vicherarr/camesp32/esp32_cam_sec/src/server.rs

use esp_idf_svc::http::server::{Configuration, EspHttpServer};
use serde::Deserialize;
use esp_idf_svc::http::Method;
use esp_idf_svc::io::Write;
use std::fs;
use std::io::Read;
use anyhow::Result;
use ::log::info;
use std::sync::{Arc, atomic::{AtomicBool, Ordering}};
use esp_idf_svc::nvs::EspDefaultNvsPartition;
use crate::config::{AppConfig, load_config, save_config};

pub struct WebServer {
    _server: EspHttpServer<'static>,
}

/// Capture one JPEG from the global esp32-camera driver. If the sensor is not
/// JPEG-native (e.g. GC0308 in RGB565), encode to JPEG in software.
fn capture_jpeg() -> Option<Vec<u8>> {
    unsafe {
        let fb = esp_idf_sys::camera_sys::esp_camera_fb_get();
        if fb.is_null() {
            return None;
        }
        let fbr = &*fb;
        let v = if fbr.format == esp_idf_sys::camera_sys::pixformat_t_PIXFORMAT_JPEG {
            if !fbr.buf.is_null() && fbr.len > 0 {
                Some(std::slice::from_raw_parts(fbr.buf, fbr.len).to_vec())
            } else {
                None
            }
        } else {
            let mut out: *mut u8 = std::ptr::null_mut();
            let mut out_len: usize = 0;
            if esp_idf_sys::camera_sys::frame2jpg(fb, 80, &mut out, &mut out_len)
                && !out.is_null()
                && out_len > 0
            {
                let jpeg = std::slice::from_raw_parts(out, out_len).to_vec();
                esp_idf_sys::camera_sys::free(out as *mut core::ffi::c_void);
                Some(jpeg)
            } else {
                None
            }
        };
        esp_idf_sys::camera_sys::esp_camera_fb_return(fb);
        v.filter(|b| !b.is_empty())
    }
}

/// Guarda el estado de alarma en NVS (preservando el modo WiFi). Ya NO reinicia: el runtime
/// híbrido aplica el cambio en vivo leyendo el flag compartido.
fn save_armed_nvs(partition: EspDefaultNvsPartition, armed: bool) {
    let (mut cfg, mut nvs) = load_config(partition);
    cfg.alarm_armed = armed;
    if let Err(e) = save_config(&mut nvs, &cfg) {
        ::log::error!("No se pudo guardar alarm_armed={}: {}", armed, e);
    }
}


macro_rules! require_auth {
    ($req:expr) => {
        if $req.header("Authorization") != Some("Basic YWRtaW46MDAxOTg5") {
            let mut response = $req.into_response(401, Some("Unauthorized"), &[("WWW-Authenticate", "Basic realm=\"CamSec\"")])?;
            response.write_all(b"Unauthorized")?;
            return Ok::<(), anyhow::Error>(());
        }
    };
}

impl WebServer {
    pub fn new(motion_state: Arc<AtomicBool>, partition: EspDefaultNvsPartition, current_mode: String, camera_ready: Arc<AtomicBool>, armed: Arc<AtomicBool>, wifi_off: Arc<AtomicBool>) -> Result<Self> {
        // uri_match_wildcard debe estar ON para que el handler "/file/*" case con
        // rutas como "/file/IMG_1.JPG"; por defecto viene desactivado (404 en la SD).
        let conf = Configuration {
            uri_match_wildcard: true,
            stack_size: 8192, // más pila: /file transmite ficheros con buffer en stack
            ..Default::default()
        };
        let mut server = EspHttpServer::new(&conf)?;

        server.fn_handler("/", Method::Get, |request| {
            require_auth!(request);
            let mut response = request.into_ok_response()?;
            let html = "<html><body><h1>ESP32-CAM Seguridad</h1>\
                <a href='/photo'>Foto en vivo</a><br/>\
                <a href='/photos'>Ver Fotos (SD)</a><br/>\
                <a href='/sensor'>Estado del Sensor</a><br/>\
                <a href='/logs'>Logs</a><hr/>\
                <form method='post' action='/deleteall' onsubmit='return confirm(\"¿Borrar TODAS las fotos de la SD?\")'>\
                <button type='submit' style='color:#b00'>Borrar TODAS las fotos SD</button></form>\
                </body></html>";
            response.write_all(html.as_bytes())?;
            Ok::<(), anyhow::Error>(())
        })?;

        // Borra todas las fotos de la SD. Usado por la app y por el botón del dashboard.
        server.fn_handler("/deleteall", Method::Post, |request| {
            require_auth!(request);
            // Recolectar nombres primero, luego borrar (no borrar mientras se itera).
            let mut names: Vec<String> = Vec::new();
            if let Ok(entries) = fs::read_dir("/sdcard") {
                for entry in entries.flatten() {
                    names.push(entry.file_name().to_string_lossy().to_string());
                }
            }
            let (mut deleted, mut errors) = (0u32, 0u32);
            for n in names {
                let path = format!("/sdcard/{}", n);
                if fs::remove_file(&path).is_ok() || fs::remove_dir_all(&path).is_ok() {
                    deleted += 1;
                } else {
                    ::log::error!("Fallo al borrar: {}", path);
                    errors += 1;
                }
            }
            info!("SD wipe: {} elementos borrados, {} errores", deleted, errors);
            let mut response = request.into_response(200, Some("OK"), &[("Content-Type", "application/json")])?;
            response.write_all(format!("{{\"deleted\":{},\"errors\":{}}}", deleted, errors).as_bytes())?;
            Ok::<(), anyhow::Error>(())
        })?;

        // Live capture: grabs one JPEG straight from the camera driver on demand.
        // Lets you verify the onboard camera over WiFi without the motion sensor.
        let cam_ready = camera_ready.clone();
        server.fn_handler("/photo", Method::Get, move |request| {
            require_auth!(request);
            if !cam_ready.load(Ordering::Relaxed) {
                let mut r = request.into_status_response(503)?;
                r.write_all(b"camera not ready")?;
                return Ok::<(), anyhow::Error>(());
            }
            match capture_jpeg() {
                Some(jpeg) => {
                    let mut response = request.into_response(200, Some("OK"), &[("Content-Type", "image/jpeg")])?;
                    response.write_all(&jpeg)?;
                }
                None => {
                    let mut response = request.into_status_response(500)?;
                    response.write_all(b"capture failed")?;
                }
            }
            Ok::<(), anyhow::Error>(())
        })?;

        // Capture on demand AND save to the SD card (used by the Android app's
        // "capturar foto" button, which does GET /capture and expects 2xx).
        let cap_ready = camera_ready.clone();
        server.fn_handler("/capture", Method::Get, move |request| {
            require_auth!(request);
            if !cap_ready.load(Ordering::Relaxed) {
                let mut r = request.into_status_response(503)?;
                r.write_all(b"camera not ready")?;
                return Ok::<(), anyhow::Error>(());
            }
            match capture_jpeg() {
                Some(jpeg) => {
                    // Nombre con fecha-hora si el reloj está puesto (LFN); si no, uptime corto.
                    let path = match crate::storage::now_stamp() {
                        Some(ts) => format!("/sdcard/{}.jpg", ts),
                        None => {
                            let secs = (unsafe { esp_idf_svc::sys::esp_timer_get_time() } / 1_000_000) % 100000;
                            format!("/sdcard/CAP{:05}.jpg", secs)
                        }
                    };
                    let saved = fs::File::create(&path)
                        .and_then(|mut f| std::io::Write::write_all(&mut f, &jpeg));
                    match saved {
                        Ok(_) => {
                            info!("Captured photo saved to {}", path);
                            let mut response = request.into_response(200, Some("OK"), &[("Content-Type", "application/json")])?;
                            response.write_all(format!("{{\"status\":\"ok\",\"file\":\"{}\"}}", path).as_bytes())?;
                        }
                        Err(e) => {
                            ::log::error!("Capture save failed: {}", e);
                            let mut response = request.into_status_response(500)?;
                            response.write_all(b"save failed")?;
                        }
                    }
                }
                None => {
                    let mut response = request.into_status_response(500)?;
                    response.write_all(b"capture failed")?;
                }
            }
            Ok::<(), anyhow::Error>(())
        })?;

        server.fn_handler("/photos", Method::Get, |request| {
            require_auth!(request);
            let mut response = request.into_ok_response()?;
            if let Ok(mut entries) = fs::read_dir("/sdcard") {
                response.write_all(b"<html><body><h2>Lista de Fotos</h2><ul>")?;
                
                let mut count = 0;
                while let Some(Ok(entry)) = entries.next() {
                    let name = entry.file_name().to_string_lossy().to_string();
                    let item = format!("<li><a href='/file/{}'>{}</a></li>", name, name);
                    if let Err(e) = response.write_all(item.as_bytes()) {
                        ::log::error!("Network write error: {}", e);
                        break;
                    }
                    count += 1;
                    if count >= 100 {
                        // Limit to 100 files to avoid massive HTML pages
                        break;
                    }
                }
                response.write_all(b"</ul></body></html>")?;
            } else {
                response.write_all(b"Error leyendo SD card")?;
            }
            Ok::<(), anyhow::Error>(())
        })?;

        server.fn_handler("/file/*", Method::Get, |request| {
            require_auth!(request);
            let uri = request.uri();
            let file_name = uri.trim_start_matches("/file/");
            let path = format!("/sdcard/{}", file_name);
            
            // Content-Type según extensión: los clips de vídeo son AVI-MJPEG.
            let lower = file_name.to_ascii_lowercase();
            let content_type = if lower.ends_with(".avi") {
                "video/x-msvideo"
            } else {
                "image/jpeg"
            };
            if let Ok(mut file) = fs::File::open(&path) {
                let mut response = request.into_response(
                    200,
                    Some("OK"),
                    &[("Content-Type", content_type)]
                )?;
                let mut buf = [0u8; 4096];
                loop {
                    match file.read(&mut buf) {
                        Ok(0) => break,
                        Ok(n) => {
                            if let Err(e) = response.write_all(&buf[..n]) {
                                ::log::error!("Network write error: {}", e);
                                break;
                            }
                        },
                        Err(e) => {
                            ::log::error!("File read error: {}", e);
                            break;
                        }
                    }
                }
            } else {
                let mut response = request.into_status_response(404)?;
                response.write_all(b"Not found")?;
            }
            Ok::<(), anyhow::Error>(())
        })?;

        let mode_clone = current_mode.clone();
        let motion_state_info = motion_state.clone();
        let armed_info = armed.clone();
        server.fn_handler("/info", Method::Get, move |request| {
            require_auth!(request);
            let is_detecting = motion_state_info.load(Ordering::Relaxed);
            let armed = armed_info.load(Ordering::Relaxed);
            // RSSI del enlace LR (dBm). 0 = sin enlace. Útil para calibrar el alcance.
            let (rssi, linked): (i32, bool) = unsafe {
                let mut ap: esp_idf_sys::wifi_ap_record_t = std::mem::zeroed();
                if esp_idf_sys::esp_wifi_sta_get_ap_info(&mut ap) == esp_idf_sys::ESP_OK {
                    (ap.rssi as i32, true)
                } else {
                    (0, false)
                }
            };
            let mut response = request.into_response(200, Some("OK"), &[("Content-Type", "application/json")])?;
            let json = format!(
                "{{\"device\": \"ESP32-CAM\", \"mode\": \"{}\", \"motion\": {}, \"rssi\": {}, \"linked\": {}, \"armed\": {}}}",
                mode_clone, is_detecting, rssi, linked, armed
            );
            response.write_all(json.as_bytes())?;
            Ok::<(), anyhow::Error>(())
        })?;
        
        // Debug log readback: returns the RAM ring buffer as plain text. This is
        // our only window once USB-OTG host mode kills the serial console.
        server.fn_handler("/logs", Method::Get, |request| {
            require_auth!(request);
            let logs = crate::logbuf::dump();
            let mut response = request.into_response(
                200,
                Some("OK"),
                &[("Content-Type", "text/plain; charset=utf-8")],
            )?;
            response.write_all(logs.as_bytes())?;
            Ok::<(), anyhow::Error>(())
        })?;

        // New endpoint to report sensor state
        let motion_state_clone = motion_state.clone();
        server.fn_handler("/sensor", Method::Get, move |request| {
            require_auth!(request);
            let is_detecting = motion_state_clone.load(Ordering::Relaxed);
            let mut response = request.into_response(
                200,
                Some("OK"),
                &[("Content-Type", "application/json")]
            )?;
            let json = format!("{{\"motion\": {}}}", is_detecting);
            response.write_all(json.as_bytes())?;
            Ok::<(), anyhow::Error>(())
        })?;
        
        // Arma/desarma la alarma en vivo (además de por BLE): fija el flag compartido + NVS.
        let arm_partition = partition.clone();
        let arm_flag = armed.clone();
        server.fn_handler("/arm", Method::Post, move |request| {
            require_auth!(request);
            arm_flag.store(true, Ordering::Relaxed);
            save_armed_nvs(arm_partition.clone(), true);
            let mut response = request.into_response(200, Some("OK"), &[("Content-Type", "application/json")])?;
            response.write_all(b"{\"status\":\"ok\",\"armed\":true}")?;
            Ok::<(), anyhow::Error>(())
        })?;

        let disarm_partition = partition.clone();
        let disarm_flag = armed.clone();
        server.fn_handler("/disarm", Method::Post, move |request| {
            require_auth!(request);
            disarm_flag.store(false, Ordering::Relaxed);
            save_armed_nvs(disarm_partition.clone(), false);
            let mut response = request.into_response(200, Some("OK"), &[("Content-Type", "application/json")])?;
            response.write_all(b"{\"status\":\"ok\",\"armed\":false}")?;
            Ok::<(), anyhow::Error>(())
        })?;

        // Cierra la sesión de media y pide volver al modo BLE (apaga WiFi, reanuda BLE).
        let wifi_off_flag = wifi_off.clone();
        server.fn_handler("/wifi_off", Method::Post, move |request| {
            require_auth!(request);
            wifi_off_flag.store(true, Ordering::Relaxed);
            info!("HTTP /wifi_off: cerrando sesión WiFi, volviendo a BLE");
            let mut response = request.into_response(200, Some("OK"), &[("Content-Type", "application/json")])?;
            response.write_all(b"{\"status\":\"ok\"}")?;
            Ok::<(), anyhow::Error>(())
        })?;

        #[derive(Deserialize)]
        struct ConfigReq {
            mode: String,
        }

        // Config endpoint
        server.fn_handler("/config", Method::Post, move |mut request| {
            require_auth!(request);
            let mut buf = [0u8; 256];
            let bytes_read = request.read(&mut buf)?;
            if bytes_read > 0 {
                let json_str = std::str::from_utf8(&buf[..bytes_read]).unwrap_or("");
                if let Ok(req) = serde_json::from_str::<ConfigReq>(json_str) {
                    let (cur, mut nvs) = load_config(partition.clone());
                    // Preservar el estado de alarma al cambiar solo el modo de red.
                    let new_config = AppConfig { mode: req.mode, alarm_armed: cur.alarm_armed };
                    if let Ok(_) = save_config(&mut nvs, &new_config) {
                        let mut response = request.into_response(200, Some("OK"), &[])?;
                        response.write_all(b"{\"status\":\"ok\"}")?;
                        
                        // Schedule restart to apply changes
                        std::thread::spawn(|| {
                            ::log::info!("Configuration saved. Rebooting in 1.5 seconds...");
                            std::thread::sleep(std::time::Duration::from_millis(1500));
                            unsafe { esp_idf_svc::sys::esp_restart() };
                        });
                        
                    } else {
                        let mut response = request.into_status_response(500)?;
                        response.write_all(b"Internal Error")?;
                    }
                } else {
                    let mut response = request.into_status_response(400)?;
                    response.write_all(b"Invalid JSON")?;
                }
            }
            Ok::<(), anyhow::Error>(())
        })?;

        info!("Web Server started");
        Ok(Self { _server: server })
    }
}
