vicherarr/camesp32/esp32_cam_sec/src/config.rs

use esp_idf_svc::nvs::{EspDefaultNvsPartition, EspNvs, NvsDefault};
use serde::{Deserialize, Serialize};
use ::log::{info, error};

#[derive(Serialize, Deserialize, Debug, Clone)]
pub struct AppConfig {
    pub mode: String, // "AP" or "STA"
    /// Estado de la alarma. Persistido en NVS para sobrevivir al deep sleep:
    /// `true` = armado (bajo consumo, graba por movimiento), `false` = desarmado (WiFi always-on).
    /// `serde(default)` mantiene compatibilidad con configuraciones guardadas antes de este campo.
    #[serde(default)]
    pub alarm_armed: bool,
}

impl Default for AppConfig {
    fn default() -> Self {
        Self {
            mode: "AP".to_string(),
            alarm_armed: false,
        }
    }
}

pub fn load_config(partition: EspDefaultNvsPartition) -> (AppConfig, EspNvs<NvsDefault>) {
    let nvs = match EspNvs::new(partition, "config", true) {
        Ok(n) => n,
        Err(e) => {
            error!("Failed to open NVS: {}", e);
            panic!("NVS error");
        }
    };
    
    let mut buf = [0u8; 512];
    if let Ok(Some(json_str)) = nvs.get_str("app_config", &mut buf) {
        if let Ok(config) = serde_json::from_str(json_str) {
            info!("Loaded config from NVS: {:?}", config);
            return (config, nvs);
        }
    }
    
    info!("Loading default config");
    (AppConfig::default(), nvs)
}

pub fn save_config(nvs: &mut EspNvs<NvsDefault>, config: &AppConfig) -> anyhow::Result<()> {
    let json_str = serde_json::to_string(config)?;
    nvs.set_str("app_config", &json_str)?;
    info!("Saved config to NVS: {}", json_str);
    Ok(())
}
